udithhaputhanthri/Constant-Current-Source-with-Feedback-Loop/FINAL_PROJECT/Circuit-PCBfiles/Buck-convertor-pcb.png

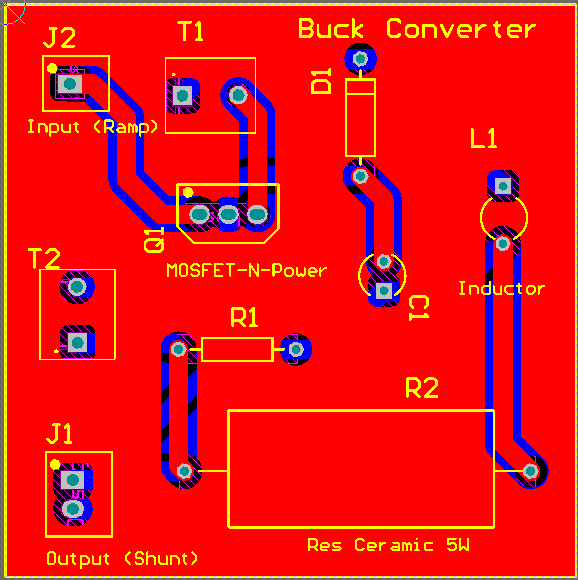
FINAL_PROJECT/Circuit-PCBfiles/Buck-convertor-pcb.png
