udithhaputhanthri/Constant-Current-Source-with-Feedback-Loop/FINAL_PROJECT/Circuit-PCBfiles/feedback-amplification-pcb.png

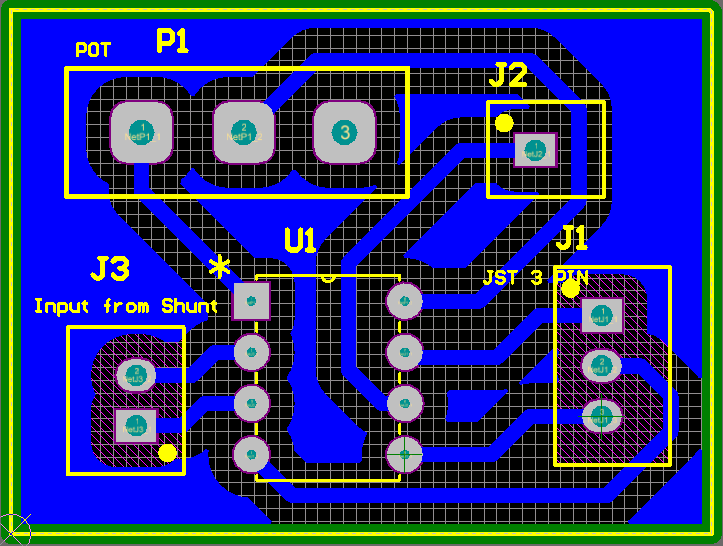
FINAL_PROJECT/Circuit-PCBfiles/feedback-amplification-pcb.png
