udithhaputhanthri/Constant-Current-Source-with-Feedback-Loop/FINAL_PROJECT/Circuit-PCBfiles/ramp-pcb.png

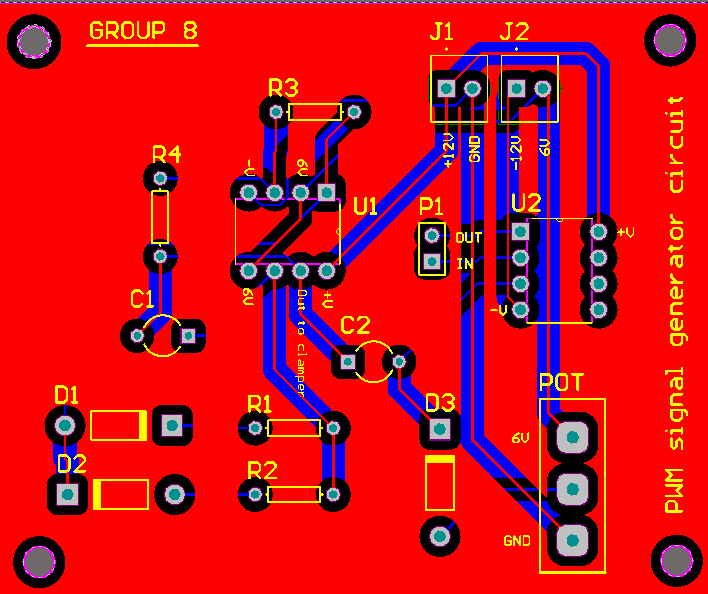
FINAL_PROJECT/Circuit-PCBfiles/ramp-pcb.png
