udithhaputhanthri/Constant-Current-Source-with-Feedback-Loop/FINAL_PROJECT/Images/Final-Circuit.png

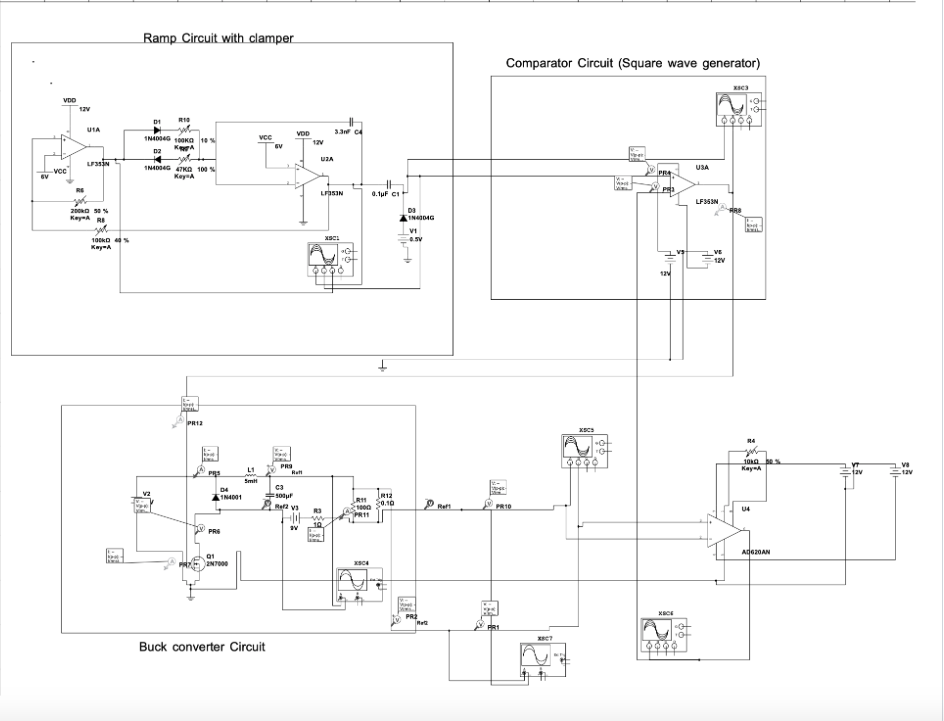
FINAL_PROJECT/Images/Final-Circuit.png
